wolf-yuan-6115/lightwolf/pumper/firmware/src/eq_dsp.h

#ifndef EQ_DSP_H_
#define EQ_DSP_H_

#include <stdbool.h>
#include <stddef.h>
#include <stdint.h>

#include "eq_config.h"

typedef struct {
  uint16_t left_peak;
  uint16_t right_peak;
  uint64_t left_square_sum;
  uint64_t right_square_sum;
} eq_level_metrics_t;

typedef struct {
  eq_level_metrics_t pre_eq;
  eq_level_metrics_t post_eq;
  uint32_t limiter_active_frames;
} eq_block_metrics_t;

// Core-1-only observer, called once per processed frame after the limiter.
// The callback must never block, allocate, or retain audio-block pointers.
void eq_set_output_observer(void (*observer)(float left, float right));
void eq_init(uint32_t sample_rate_hz, eq_config_t const *config);
void eq_set_sample_rate(uint32_t sample_rate_hz);
void eq_reset_state(void);
bool eq_set_config(eq_config_t const *config);
void eq_process_interleaved_stereo(float *restrict interleaved, size_t frame_count,
                                   eq_block_metrics_t *metrics, bool measure_rms);

#endif
